charlie-x/LayerOne2023/keyboard.h

/* Microchip Technology Inc. and its subsidiaries.  You may use this software 
 * and any derivatives exclusively with Microchip products. 
 * 
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
 * IN NO EVENT WILL MICROCHIP BE LIABLE FOR ANY INDIRECT, SPECIAL, PUNITIVE, 
 * INCIDENTAL OR CONSEQUENTIAL LOSS, DAMAGE, COST OR EXPENSE OF ANY KIND 
 * WHATSOEVER RELATED TO THE SOFTWARE, HOWEVER CAUSED, EVEN IF MICROCHIP HAS 
 * BEEN ADVISED OF THE POSSIBILITY OR THE DAMAGES ARE FORESEEABLE.  TO THE 
 * FULLEST EXTENT ALLOWED BY LAW, MICROCHIP'S TOTAL LIABILITY ON ALL CLAIMS 
 * IN ANY WAY RELATED TO THIS SOFTWARE WILL NOT EXCEED THE AMOUNT OF FEES, IF 
 * ANY, THAT YOU HAVE PAID DIRECTLY TO MICROCHIP FOR THIS SOFTWARE.
 *
 * MICROCHIP PROVIDES THIS SOFTWARE CONDITIONALLY UPON YOUR ACCEPTANCE OF THESE 
 * TERMS. 
 */

/* 
 * File:   
 * Author: 
 * Comments:
 * Revision history: 
 */

// This is a guard condition so that contents of this file are not included
// more than once.  
#ifndef XC_KEYBOARD_H
#define	XC_KEYBOARD_H

#include <xc.h> // include processor files - each processor file is guarded.  
#include <htc.h>

#include "Usb.h"
#include "ws2812.h"
#include "scan_codes.h"
// TODO Insert appropriate #include <>

// TODO Insert C++ class definitions if appropriate

// TODO Insert declarations

// Comment a function and leverage automatic documentation with slash star star
/**
    <p><b>Function prototype:</b></p>
  
    <p><b>Summary:</b></p>

    <p><b>Description:</b></p>

    <p><b>Precondition:</b></p>

    <p><b>Parameters:</b></p>

    <p><b>Returns:</b></p>

    <p><b>Example:</b></p>
    <code>
 
    </code>

    <p><b>Remarks:</b></p>
 */
// TODO Insert declarations or function prototypes (right here) to leverage 
// live documentation

#ifdef	__cplusplus
extern "C" {
#endif /* __cplusplus */


#define _bitTest(bit)                    (1 << (bit))
#define is_bit_set(sfr,bit)         ((sfr) & _bitTest(bit)) 

// Local Defines

#define WS2812              RC3
#define Button              RA4 // RA4 for new version, RC4 for old version
#define Led                 RC5
    
    // TODO If C++ is being used, regular C code needs function names to have C 
    // linkage so the functions can be used by the c code. 

    void ascii2scan(BYTE ascii, BYTE ledState, BYTE* modifier, BYTE* keycode);
    size_t print(const BYTE *buffer);
    //int strlen(char *str);
    unsigned char typeChar(BYTE ascii);
    void pressKey(BYTE modifiers, BYTE keycode1, BYTE keycode2, BYTE keycode3, BYTE keycode4, BYTE keycode5, BYTE keycode6);
    BYTE getLEDstate(void);
    void PrepareHidTxBuffer(void);
    BYTE value2hex( BYTE value );
    void pressKeyOnly(BYTE modifiers, BYTE keycode1, BYTE keycode2, BYTE keycode3, BYTE keycode4, BYTE keycode5, BYTE keycode6);
    
#ifdef	__cplusplus
}
#endif /* __cplusplus */

#endif	/* XC_KEYBOARD_H */
