charlie-x/LayerOne2023/system.h

/******************************************************************************/
/* System Level #define Macros                                                */
/******************************************************************************/

/* TODO Define system operating frequency */

/* Microcontroller MIPs (FCY) */
#define SYS_FREQ        500000L
#define FCY             SYS_FREQ/4

/******************************************************************************/
/* System Function Prototypes                                                 */
/******************************************************************************/

/* Custom oscillator configuration functions, reset source evaluation
functions, and other non-peripheral microcontroller initialization functions
go here. */

void ConfigureOscillator(void); /* Handles clock switching/osc initialization */
